ZT-715/avr-asm-weighing-scale/boards/ia.asc

R1: res; 10k
R2: res; 10k
R5: res; 1k
R6: res; 100k
R7: res; 100k
R8: res; 100k
U1: LT1001
U2: LT1001
V1: voltage; 15
V2: voltage; 15
V3: voltage; 1m
Named nets: -15, 15, 0
.op
