ZT-715/avr-asm-weighing-scale/LUT.asm

.cseg
LUT_kg: .db "0.0   ",0,0,"0.005 ",0,0,"0.01  ",0,0,"0.015 ",0,0,"0.02  ",0,0,"0.024 ",0,0,"0.029 ",0,0,"0.034 ",0,0,"0.039 ",0,0,"0.044 ",0,0,"0.049 ",0,0,"0.054 ",0,0,"0.059 ",0,0,"0.063 ",0,0,"0.068 ",0,0,"0.073 ",0,0,"0.078 ",0,0,"0.083 ",0,0,"0.088 ",0,0,"0.093 ",0,0,"0.098 ",0,0,"0.103 ",0,0,"0.107 ",0,0,"0.112 ",0,0,"0.117 ",0,0,"0.122 ",0,0,"0.127 ",0,0,"0.132 ",0,0,"0.137 ",0,0,"0.142 ",0,0,"0.146 ",0,0,"0.151 ",0,0,"0.156 ",0,0,"0.161 ",0,0,"0.166 ",0,0,"0.171 ",0,0,"0.176 ",0,0,"0.181 ",0,0,"0.186 ",0,0,"0.19  ",0,0,"0.195 ",0,0,"0.2   ",0,0,"0.205 ",0,0,"0.21  ",0,0,"0.215 ",0,0,"0.22  ",0,0,"0.225 ",0,0,"0.229 ",0,0,"0.234 ",0,0,"0.239 ",0,0,"0.244 ",0,0,"0.249 ",0,0,"0.254 ",0,0,"0.259 ",0,0,"0.264 ",0,0,"0.269 ",0,0,"0.273 ",0,0,"0.278 ",0,0,"0.283 ",0,0,"0.288 ",0,0,"0.293 ",0,0,"0.298 ",0,0,"0.303 ",0,0,"0.308 ",0,0,"0.312 ",0,0,"0.317 ",0,0,"0.322 ",0,0,"0.327 ",0,0,"0.332 ",0,0,"0.337 ",0,0,"0.342 ",0,0,"0.347 ",0,0,"0.352 ",0,0,"0.356 ",0,0,"0.361 ",0,0,"0.366 ",0,0,"0.371 ",0,0,"0.376 ",0,0,"0.381 ",0,0,"0.386 ",0,0,"0.391 ",0,0,"0.396 ",0,0,"0.4   ",0,0,"0.405 ",0,0,"0.41  ",0,0,"0.415 ",0,0,"0.42  ",0,0,"0.425 ",0,0,"0.43  ",0,0,"0.435 ",0,0,"0.439 ",0,0,"0.444 ",0,0,"0.449 ",0,0,"0.454 ",0,0,"0.459 ",0,0,"0.464 ",0,0,"0.469 ",0,0,"0.474 ",0,0,"0.479 ",0,0,"0.483 ",0,0,"0.488 ",0,0,"0.493 ",0,0,"0.498 ",0,0,"0.503 ",0,0,"0.508 ",0,0,"0.513 ",0,0,"0.518 ",0,0,"0.522 ",0,0,"0.527 ",0,0,"0.532 ",0,0,"0.537 ",0,0,"0.542 ",0,0,"0.547 ",0,0,"0.552 ",0,0,"0.557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

 
.equ LUT_str_len = 4 ; 2 characters/byte
 
set_LUT_kg: ;receive index in r17:r16 and sets Z 
  ldi ZL, low(LUT_kg << 1)
  ldi ZH, high(LUT_kg << 1)

  ret

set_LUT_lb: ;receive index in r17:r16 and sets Z 
  ldi ZL, low(LUT_lb << 1)
  ldi ZH, high(LUT_lb << 1)

  ret
